MG-Jang/SAMSUNG-IOT-ROBOT-PJT-BOBI/HW/WAVEGO/version_0/코드 수정 후 적용.md

# 코드 수정 및 적용

- camera_opencv.py
- line:541
- robot.lookUp()을 여러번 추가하여 실제로 앉는 것 처럼 보여줌
```
elif act == 'up':
robot.lookUp()
robot.lookUp()
robot.lookUp()
robot.lookUp()
robot.lookUp()
robot.lookUp()
robot.lookUp()
```
