MG-Jang/SAMSUNG-IOT-ROBOT-PJT-BOBI/HW/DOCS/tips/[voice] setting_USB_mic.md

## USB 마이크 설정

USB 마이크를 라즈베리파이에 사용하기 위해서는 SW 혹은 패키지 따로 설치 안해줘도 된다.

우선, USB 마이크를 라즈베리파이 USB 포트에 연결한다.
다음 명령어를 통해 연결된 Port를 확인한다.
```
arecord -l
```
다음 이미지를 확인하면, card 2 즉 `2번 포트`에 USB 마이크가 꽂혀있는 것을 알 수 있다.

	
### USB 마이크 테스트

```
arecord --device=hw:2,0 --format S16_LE --rate 44100 -V mono -c1 voice.wav
```

> --device=hw:2는 2번 포트에 연결되어 있어 다음과 같이 작성했다.
voice.wav라는 파일에 음성파일 저장

해당 명령어를 실행시키면, `voice.wav`라는 파일이 생성되고, 해당 파일을 `mobaxterm` 좌측에서 더블클릭 혹은 윈도우로 복사 후 재생시켰다.

### 이슈 및 해결책
음성 녹음을 할 때, `볼륨이 매우 작은` 상태로 녹음이 되었다.
녹음 음량을 높일 수 있는 방법을 검색하여 해결책을 찾을 수 있었다.
 ```
 alsamixer
 ```
 을 통해 마이크 음량 조절가능하다.
 F6으로 오디오 선택 후 F5로 전체 조회 후 마우스 클릭으로 조절 가능하다.
