MG-Jang/SAMSUNG-IOT-ROBOT-PJT-BOBI/HW/DOCS/tips/[WAVEGO]senor_where_to_buy.md

# 센서 가격및 구매처

> 구매처: 송파 메이커스 페이스 (배송비 2700원)
- oled센서 i2c버전 2개: 3390*2
  - https://smartstore.naver.com/makerspace/products/2006471559

- ~~oled센서 spi버전(싸피1학기 떄 사용했던 것) : 4300 * 2~~
  - https://smartstore.naver.com/makerspace/products/2006472607

- 가스센서: 1980
  - https://smartstore.naver.com/makerspace/products/2006429718

- 터치센서: 300
  - https://smartstore.naver.com/makerspace/products/2667722657

- 스피커 지름 20mm : 200 (작동할지 모르겠지만 가격 리스크x)
  - https://smartstore.naver.com/makerspace/products/5784106870

- ~~DHT11(온습도 센서): 2000~~
  - https://smartstore.naver.com/makerspace/products/5010083549

추가 구매 사항
- 구리 방열판
- 빵판?
- 3핀

# wifi수신기

- http://itempage3.auction.co.kr/DetailView.aspx?ItemNo=C403515088&frm3=V2
  - 가격: 22400 무료 배송 
  - 장점:
    - 색상이 검정색이기 때문에 강아지 색상과도 일치
    - 크기가 작음
    - 광고 자체가 jetson nano 우분투 등 소형 컴퓨터 wifi수신기로 광고
    - 드라이버 설치x
    - 정확히 중앙에 있어 꼬리사용시 미관상 우수
  - 단점:
    - 기기명이 정확히 안나와있음.
    - 설명이 중국어로 적혀있어 의심이좀 감
  
- https://smartstore.naver.com/cotini/products/5220972886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
  - 가격: 19900 +3000(배송비)  // 현재 구매한다면 이제품을 생각
  - 장점: 
    - iptime 제조사이기 때문에 신뢰성 높음
    - 크기 작음
    - 드라이버 설치x
  - 단점:
    - 색상이 흰색이다.
    - 중앙 정렬이 약간 안되어있음.(봐줄만은 함)

- https://search.shopping.naver.com/catalog/26921391522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
  - 가격: 23400 + 3000(배송비 추정) 
    - 장점:
      - <span style="color:orange">가장 예쁘다!!!!!!. </span>
      - 브랜드 신뢰성 높음
      - wifi속도 가장 빠름
    - 단점:
      - 드라이버 설치가 필수!!!!!!!!!!!
      - 조금 비쌈?

# 스피커 
- https://www.coupang.com/vp/products/1421453945?itemId=2459973542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

# 라즈베리파이용 18650 배터리 쉴드
- 용도: 로봇에 장착된 배터리를 이용하여 esp32와 라즈베리파이가 통신할경우 통신에 문제가 발생하는 경우가 많다.(라즈베리파이에 충분한 전압이 공급되지 못하는 점과 gpio핀을 통해 공급하기 때문에 안정성도 떨어진다.) 따라서 추가 전력공급장치를 연결하여 안정적으로 라즈베리파이와 esp32가 통신 할 수 있도록 해준다.
-  https://smartstore.naver.com/bearfabmall/products/5240362851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
   -  특징
   -  배터리 1구
   -  무게 약 50~ 55g (배터리 포함) 
   -  no off가 가능할지? 

- https://smartstore.naver.com/makerspace/products/3537364484
  - 특징
    - 배터리 1구
    - on off 탑재
