MG-Jang/SAMSUNG-IOT-ROBOT-PJT-BOBI/HW/SENSORS/version_0/sensor pin.txt

OLED SDA : 2핀
SCL : 3핀

GAS : 15핀
DHT11 : 18핀
touch : 14핀

.
