MG-Jang/SAMSUNG-IOT-ROBOT-PJT-BOBI/HW/DOCS/ideas/[idea] web_essential_tech.md

### WEB

- 형태 : 웹 앱
- 타겟 사용자 : 부모님
- 기술스택
  - FE : HTML5, CSS3, Javascript, React.js, Node.js, PWA
  - BE : Python, Django
  - Server : MySQL, AWS S3
- 로그인
  - Google Login API
    - 영상을 스트리밍할 유튜브 계정 연동
  - 자체제작 로그인 API
- 1계정 1로봇 1디바이스
- qr코드를 통해 계정과 로봇과 연동
  - 가능한 경우 - 그렇지 않으면 연결 상태 일단 가정
- 기능
  - 기초 페이지
    - 앱 하단에 음성전송 토글을 활성화하면 앱 사용자가 음성을 녹음하고 비활성화하면 음성파일 형태로 서버에 저장하고 저장된 음성을 로봇에서 재생함 (카톡음성메시지랑 비슷한데 따로 재생버튼 안누르고 음성이 바로 나오는?)
      - 로봇에게 직접 통신으로 메시지를 보냈고 보낸 메시지 path 보내주기
    - 앱 상단에 실시간 로봇 배터리 잔량 표시기능 (충전 중일때는 잔량 표시없이 충전 중이라고만 표시할지)
  - 조작 페이지에서 로봇 전후좌우 이동 조작 가능 (기기와 직접 연결_인터넷)
    - 기초 조작: 좌/우/전진/후진 버튼 필요 (십자버튼)
      - 좌우-방향전환
      - 전후-전진/후진
    - 로봇에게 직접 통신으로 보내주기
  - 영상 스트리밍 기능
    - 유투브 계정과 연동
    - 웹캠으로 받아온 영상과 마이크로 받아온 음성을 합쳐서 유투브 라이브 형태로 실시간으로 스트리밍해서 보여주기 (음성 + 영상 합치는게 되는지 일단 해보자구)
  - 아카이브 기능
    - 스트리밍중인 영상을 실시간으로 캡처하여 아카이브에 저장하는 기능 ⇒가능? (기술 알아보기)
    - 스트리밍된 영상을 개인 유투브 스튜디오에서 편집해서 저장하고 저장된 영상의 링크와 그 영상의 썸네일을 아카이브 형태로 저장
  - 아이가 로봇을 통해 보낸 음성 메시지 조회 페이지 (미확인/확인 분류, 알림 팝업?)
    - 로봇에서 S3로 보낸 음성 메시지를 받아와 화면에서 출력
    - 로봇에서 새로운 메시지 알림을 받는 경우 데이터를 읽어오고 사용자에게 알림
  - 센서로 받아온 실시간 데이터를 보여주는 페이지
    - 현재 온도와 습도
    - 30분에 한 번  실시간으로 최신 데이터 출력
    - 일정 주기(30분? 1시간?)마다 저장된 온습도 값을 특정 기간동안 그래프 형태로 보여주는 기능
    - 가스 센서 - 1분마다 갱신되는 센서값에서 유해 가스값이 비정상적으로 높으면 반응(alert)
  - 로봇과의 친밀도를 나타내는 페이지
    - 특정 행동을 하면 친밀도 경험치가 쌓임
    - 경험치가 어느 정도 쌓이면 친밀도 레벨이 올라감
    - 친밀도 레벨에 따라 스토리와 가능한 행동들을 보여줌
    - 친밀도 레벨이 올라감에 따라 스토리와 로봇이 가능한 행동들이 점점 해금됨
    - 가능한 행동 리스트를 클릭하면 로봇이 그 행동을 하는 영상을 보여줌 (사전에 영상 녹화하여 삽입 (영상은 s3에 저장))
    - 1분마다 DB에 친밀도 update
  - 환경설정 페이지
    - 앱 테마 설정 : 기본모드 / 다크모드
    - 절전모드 설정 : 활성화시 로봇은 영상촬영을 비롯한 모든 행동을 멈추고 영상 촬영 및 스트리밍 진행과 눈 부분에 부착된 OLED에서 현재 시간만 보여줌
      - 절전모드 활성화, 비활성화 로봇에게 직접 통신으로 보내줌
    - 보비 음량 설정 : 보비 목소리 크기 조절
