MG-Jang/SAMSUNG-IOT-ROBOT-PJT-BOBI/DOCS/etc/bobi_always.jpg

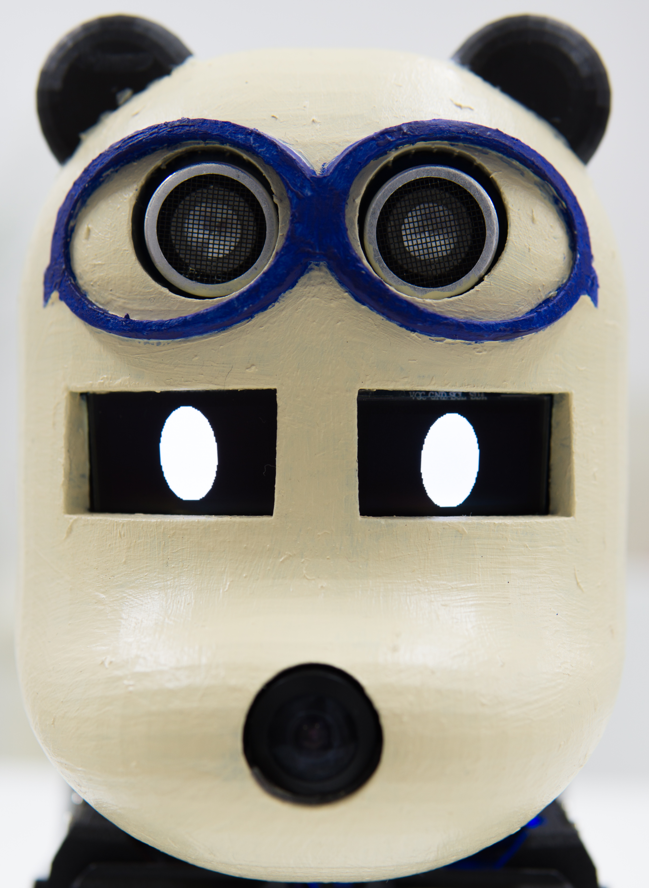
DOCS/etc/bobi_always.jpg
