MG-Jang/SAMSUNG-IOT-ROBOT-PJT-BOBI/DOCS/etc/bobi_mssg_fail.jpg

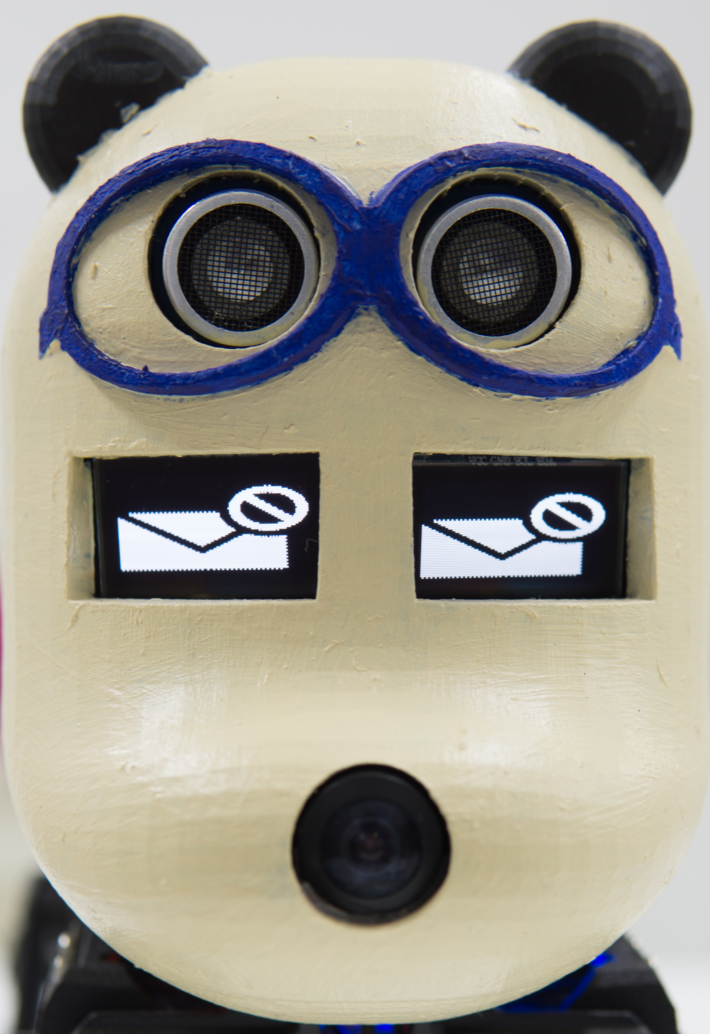
DOCS/etc/bobi_mssg_fail.jpg
