MG-Jang/SAMSUNG-IOT-ROBOT-PJT-BOBI/DOCS/etc/bobi_mssg_success.jpg

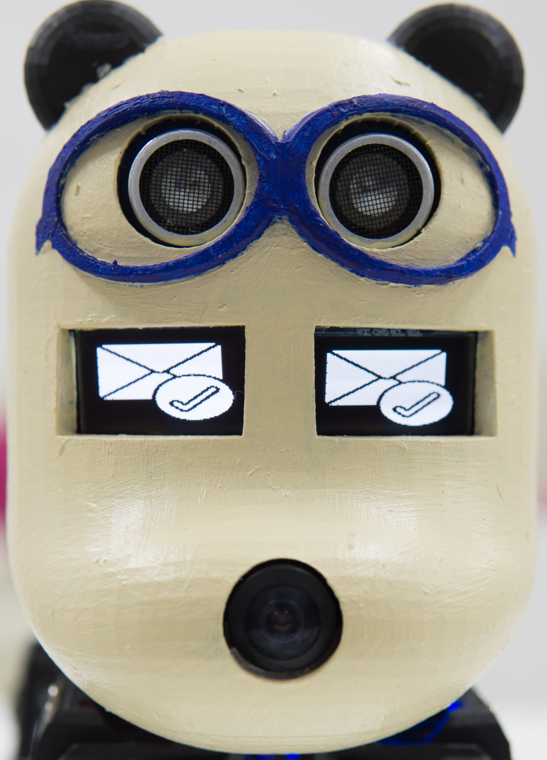
DOCS/etc/bobi_mssg_success.jpg
