MG-Jang/SAMSUNG-IOT-ROBOT-PJT-BOBI/DOCS/etc/bobi_smile.jpg

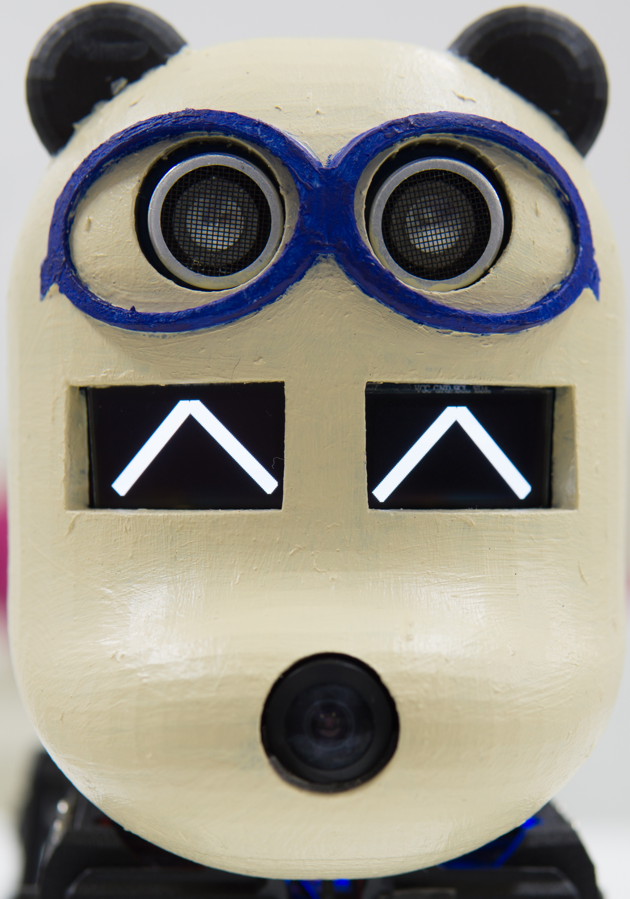
DOCS/etc/bobi_smile.jpg
