MG-Jang/SAMSUNG-IOT-ROBOT-PJT-BOBI/DOCS/etc/단체사진.jpg

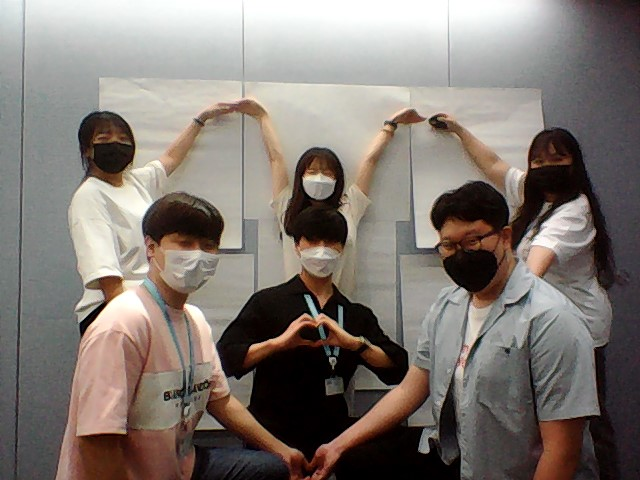
DOCS/etc/단체사진.jpg
