MG-Jang/SAMSUNG-IOT-ROBOT-PJT-BOBI/DOCS/etc/팀에게_바라는_점.jpg

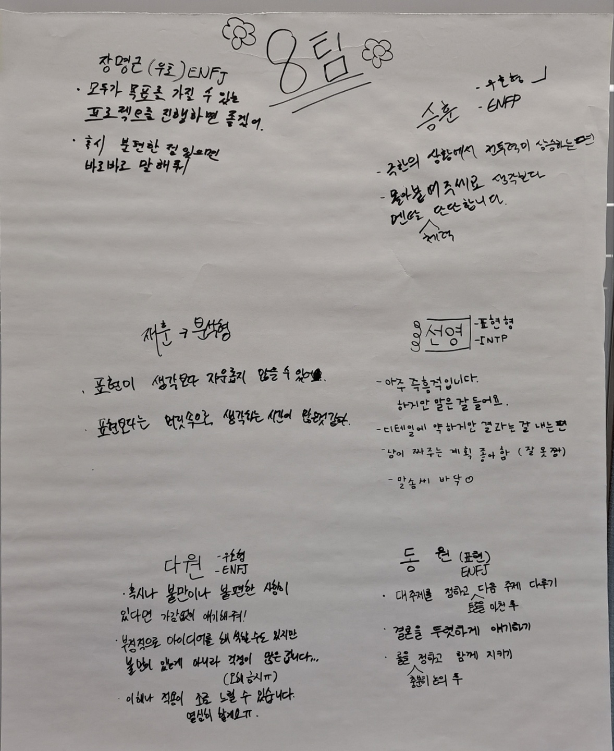
DOCS/etc/팀에게_바라는_점.jpg
