MG-Jang/SAMSUNG-IOT-ROBOT-PJT-BOBI/DOCS/ideas/[appearance] bobi_idea1.jpg

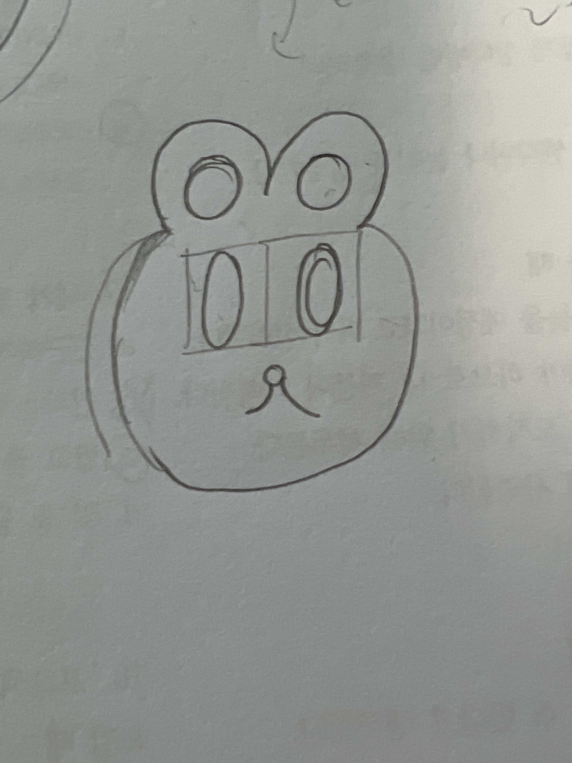
DOCS/ideas/[appearance] bobi_idea1.jpg
