MG-Jang/SAMSUNG-IOT-ROBOT-PJT-BOBI/DOCS/ideas/[appearance] bobi_idea2.jpg

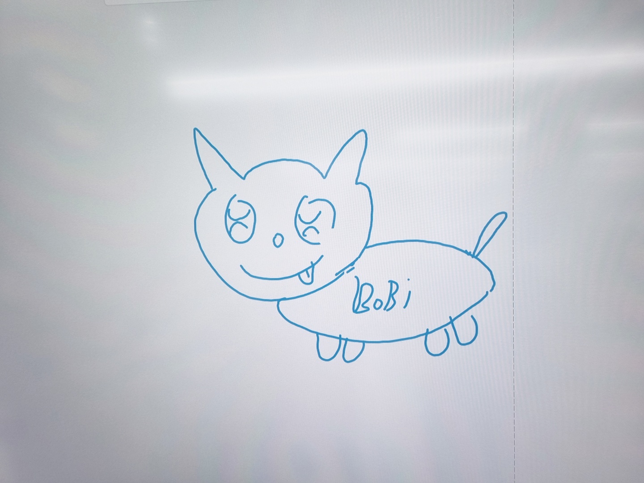
DOCS/ideas/[appearance] bobi_idea2.jpg
