MG-Jang/SAMSUNG-IOT-ROBOT-PJT-BOBI/DOCS/ideas/[appearance] bobi_idea4.jpg

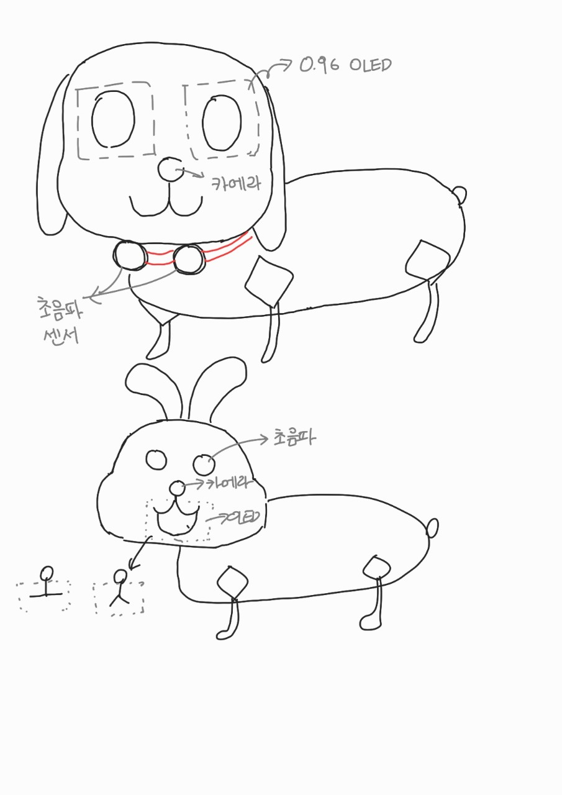
DOCS/ideas/[appearance] bobi_idea4.jpg
