MG-Jang/SAMSUNG-IOT-ROBOT-PJT-BOBI/DOCS/ideas/[appearance] bobi_idea5.jpg

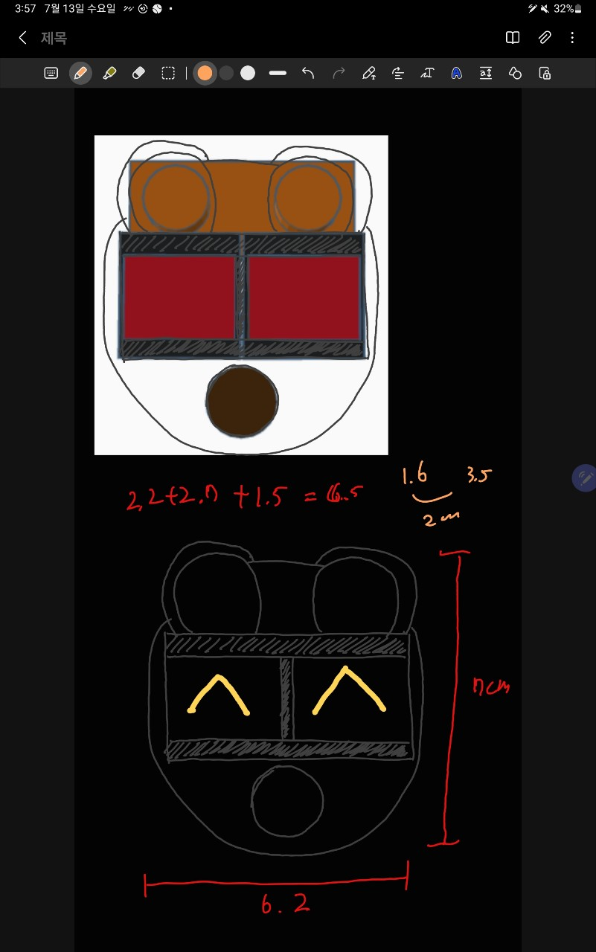
DOCS/ideas/[appearance] bobi_idea5.jpg
