MG-Jang/SAMSUNG-IOT-ROBOT-PJT-BOBI/DOCS/ideas/[DB] 0718_ERD.png

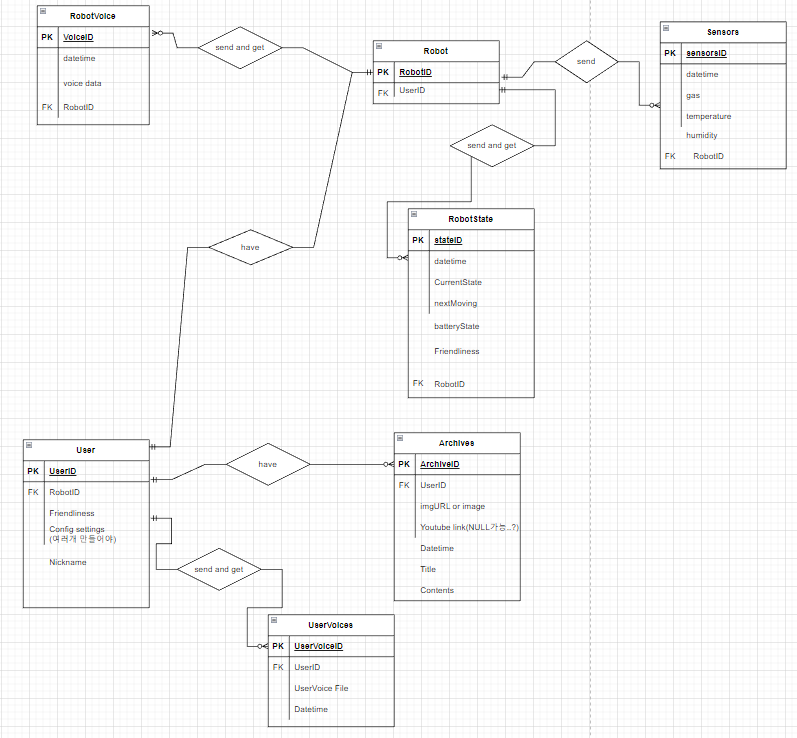
DOCS/ideas/[DB] 0718_ERD.png
