MG-Jang/SAMSUNG-IOT-ROBOT-PJT-BOBI/DOCS/ideas/[DB] 0719_ERD.jpg

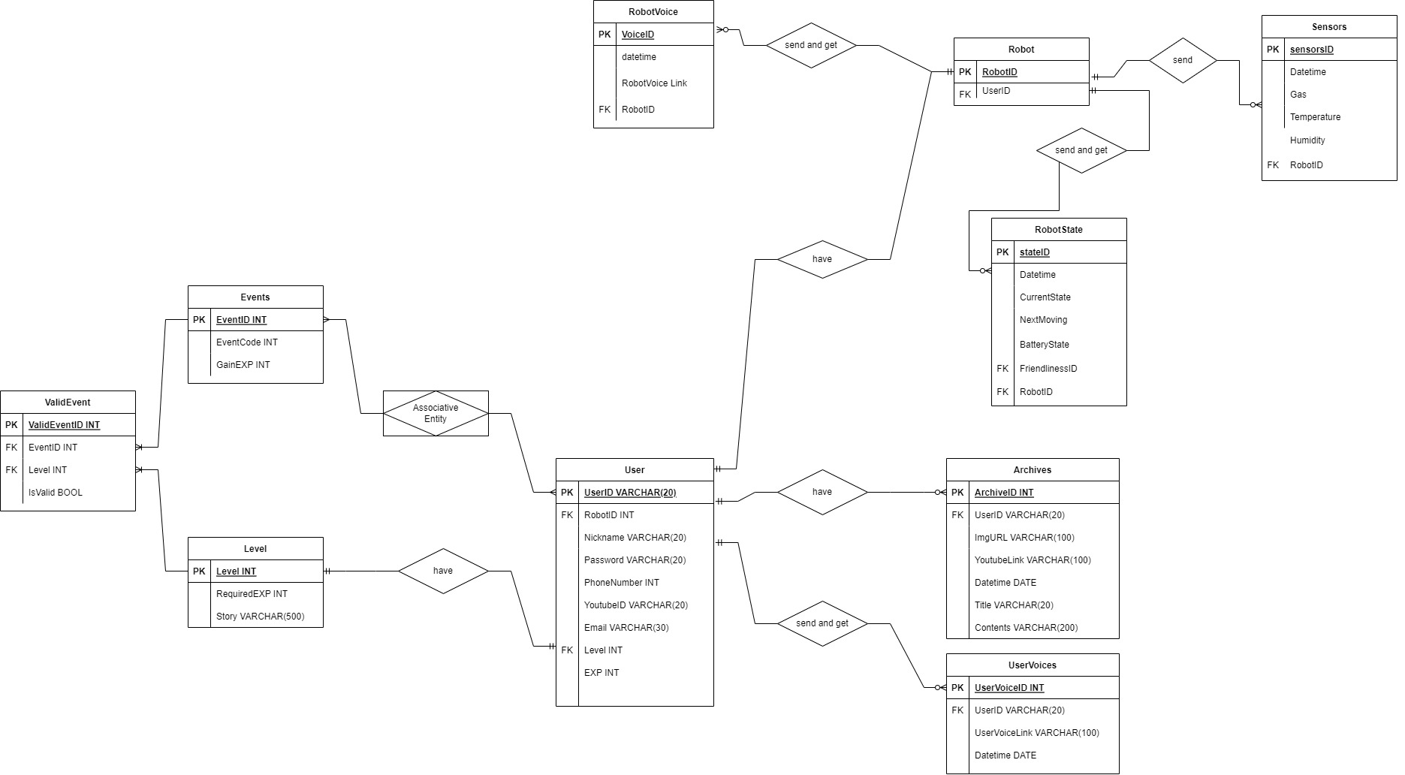
DOCS/ideas/[DB] 0719_ERD.jpg
