MG-Jang/SAMSUNG-IOT-ROBOT-PJT-BOBI/WEB/BE/README.assets/image-20220818151705240.png

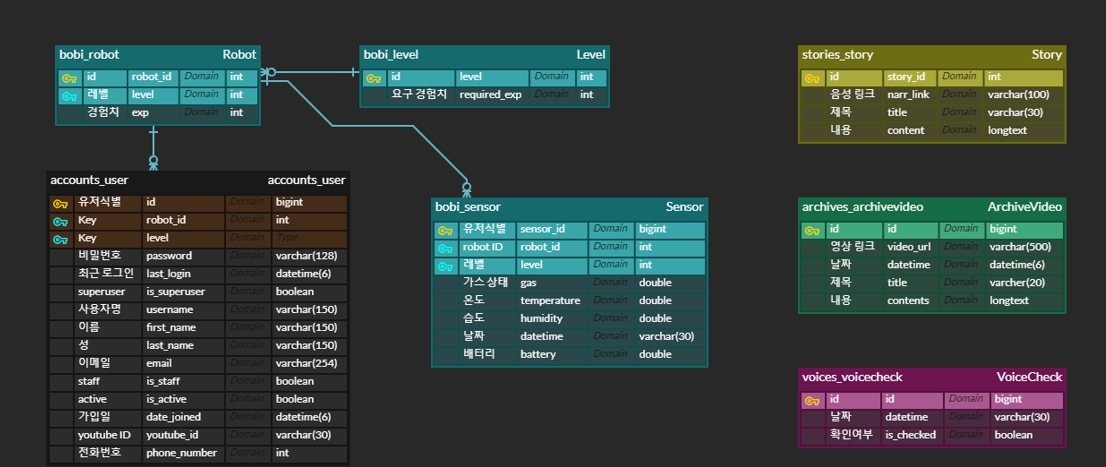
WEB/BE/README.assets/image-20220818151705240.png
