MG-Jang/SAMSUNG-IOT-ROBOT-PJT-BOBI/WEB/BE/README.assets/image-20220818172745645.png

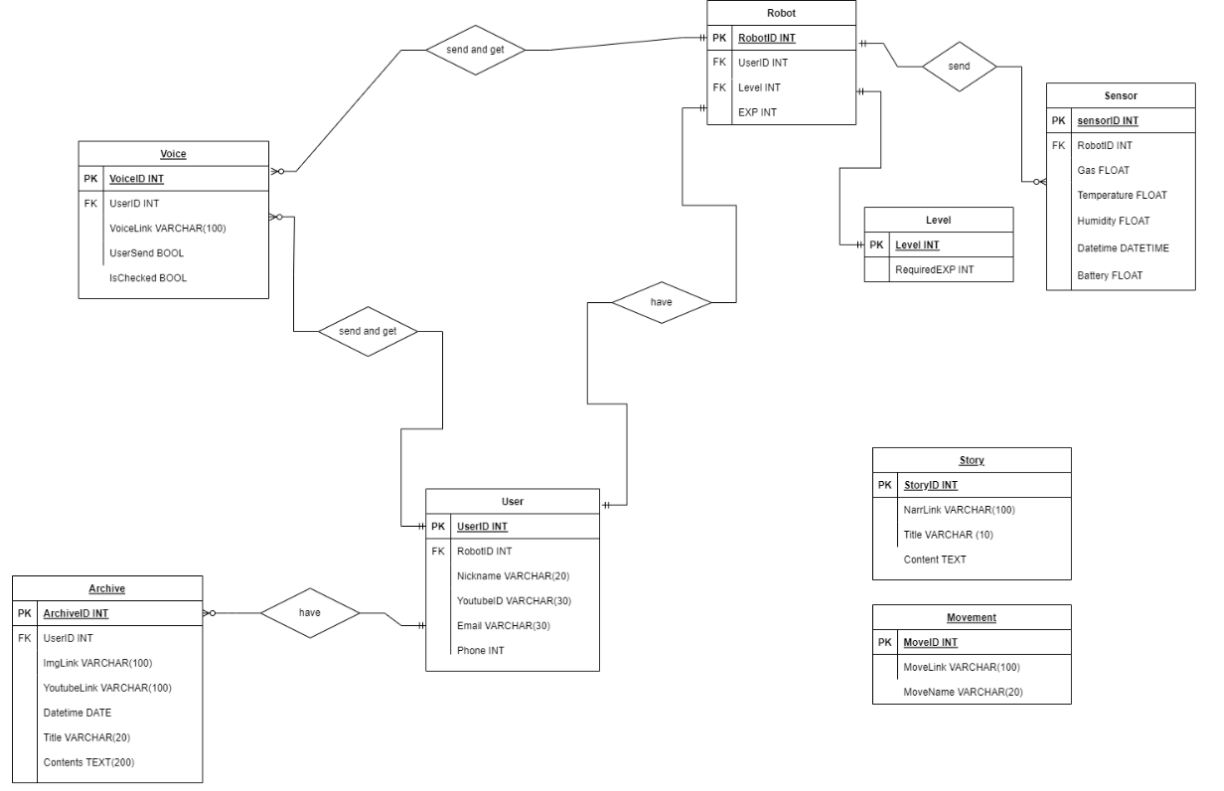
WEB/BE/README.assets/image-20220818172745645.png
