MG-Jang/SAMSUNG-IOT-ROBOT-PJT-BOBI/WEB/FE + BE/bobi_backup/README.assets/image-20220818011454465.png

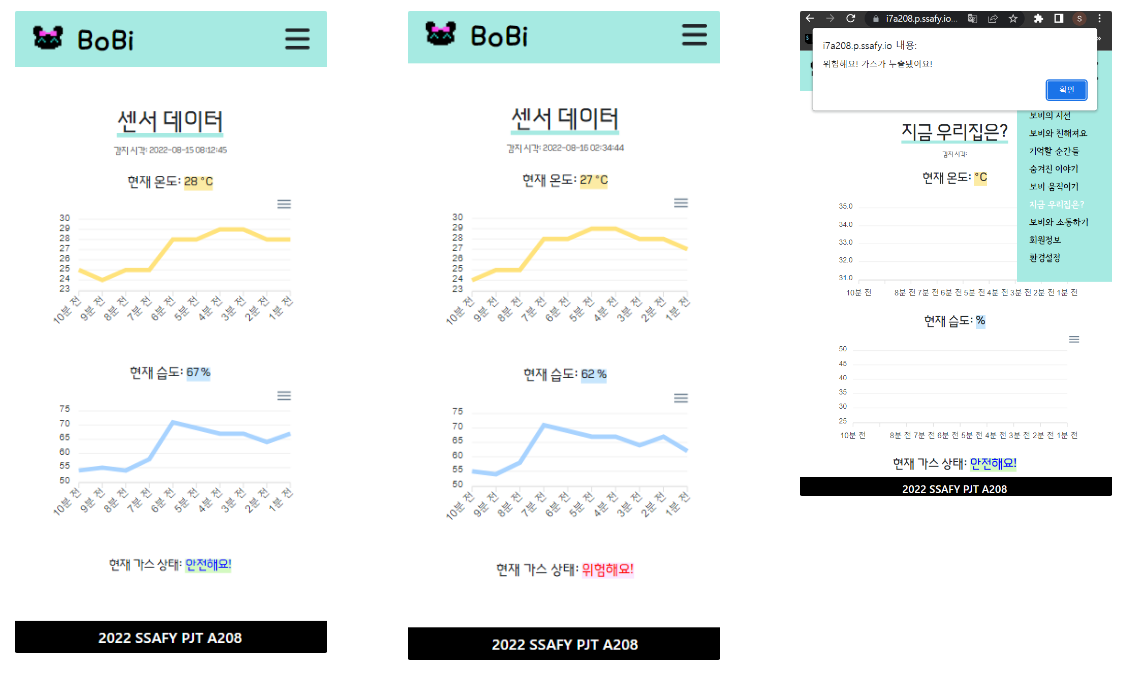
WEB/FE + BE/bobi_backup/README.assets/image-20220818011454465.png
