MG-Jang/SAMSUNG-IOT-ROBOT-PJT-BOBI/WEB/FE/DOCS/ideas/[layout] 0714_initial_layout.png

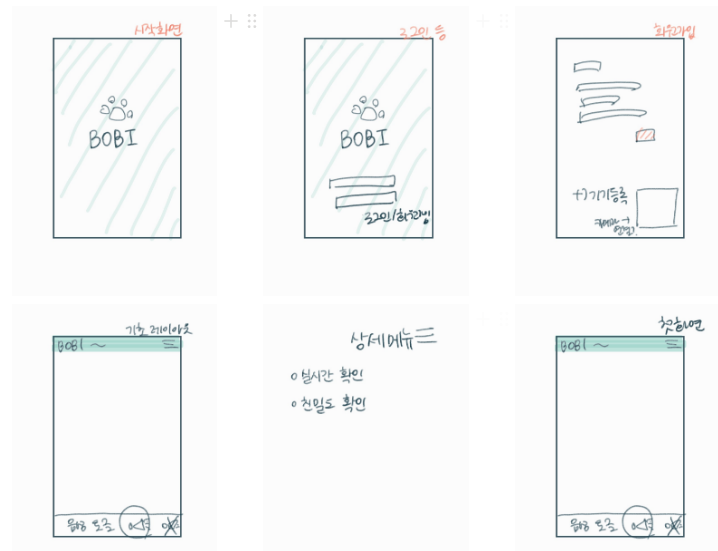
WEB/FE/DOCS/ideas/[layout] 0714_initial_layout.png
