MG-Jang/SAMSUNG-IOT-ROBOT-PJT-BOBI/WEB/FE/DOCS/ideas/[layout] 0714_pages.jpg

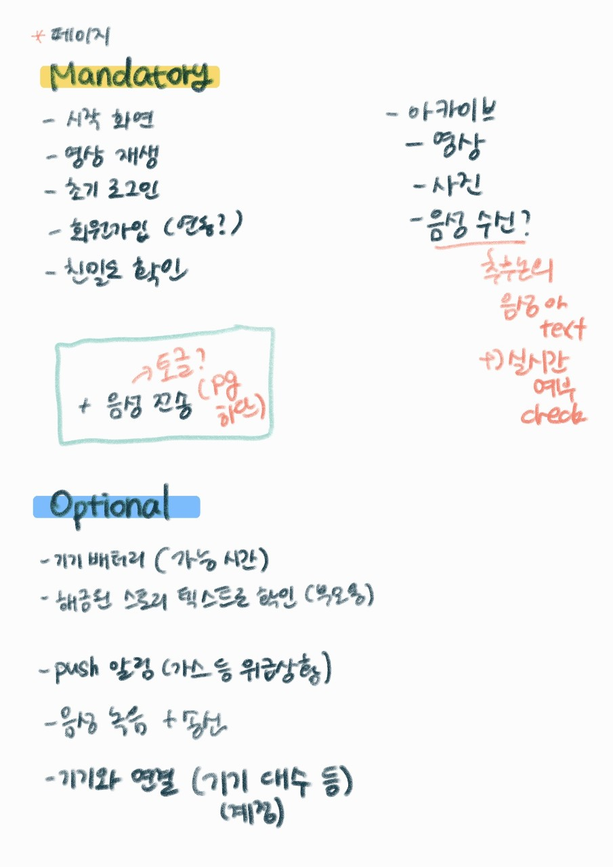
WEB/FE/DOCS/ideas/[layout] 0714_pages.jpg
