MG-Jang/SAMSUNG-IOT-ROBOT-PJT-BOBI/WEB/FE/README.assets/image-20220818002039471.png

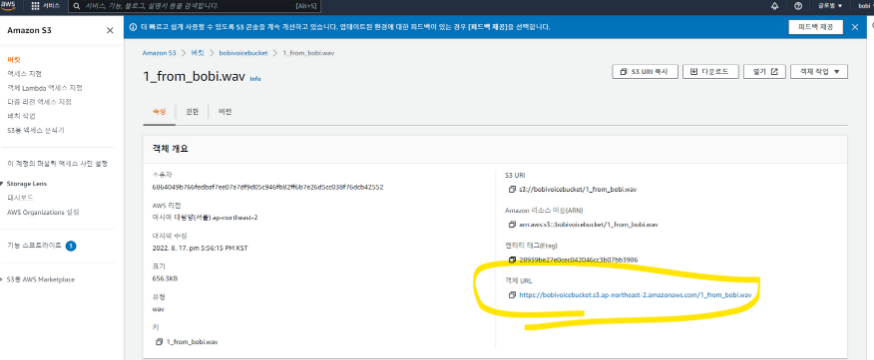
WEB/FE/README.assets/image-20220818002039471.png
