MG-Jang/SAMSUNG-IOT-ROBOT-PJT-BOBI/WEB/README.assets/image-20220819102034384.png

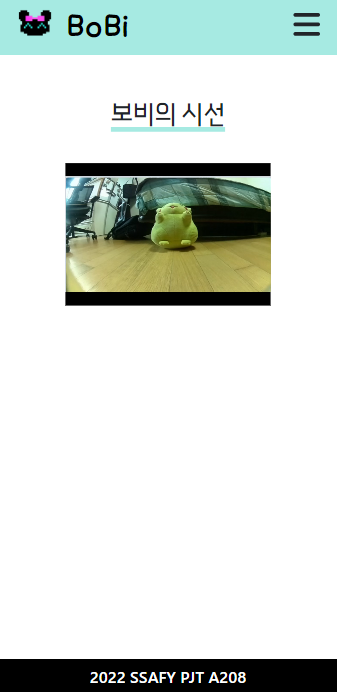
WEB/README.assets/image-20220819102034384.png
