MG-Jang/SAMSUNG-IOT-ROBOT-PJT-BOBI/DOCS/tips/[git] basic_guide.assets/image-20220711194625866.png

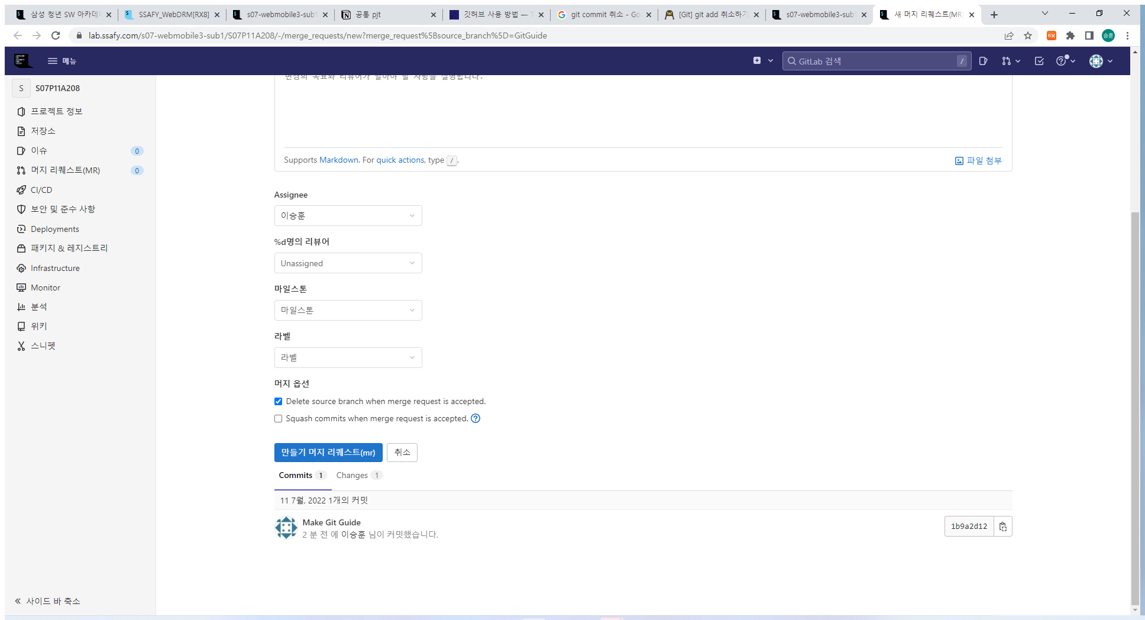
DOCS/tips/[git] basic_guide.assets/image-20220711194625866.png
