MG-Jang/SAMSUNG-IOT-ROBOT-PJT-BOBI/DOCS/tips/[git] basic_guide.assets/image-20220711195616462.png

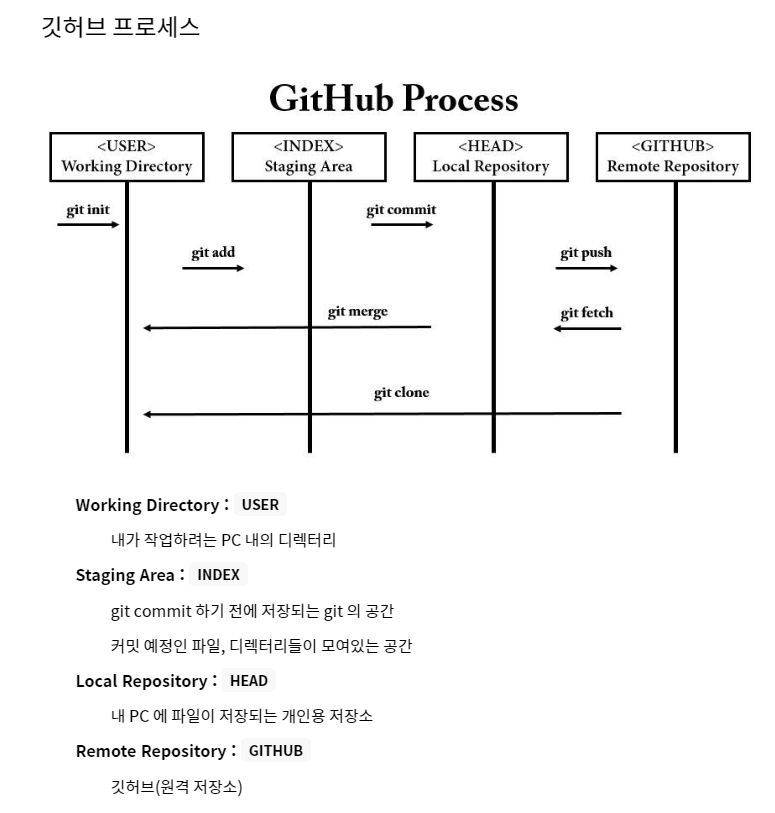
DOCS/tips/[git] basic_guide.assets/image-20220711195616462.png
