MG-Jang/SAMSUNG-IOT-ROBOT-PJT-BOBI/HW/VOICE_DETECTION/voice.py

import os
import voice_porcupine_custom
import sys
import time
from threading import Thread
from voice_recognition import VoiceRecognition


class DetectHotword(Thread):
    def __init__(self, user_id):
        Thread.__init__(self)
        self.kill_received = False
        self.user_id = user_id
        self.stt = VoiceRecognition(self.user_id)
    def run(self):
        while not self.kill_received:
            if(voice_porcupine_custom.hot_word_flag):
                print("Hotword detected")
                self.stt.run()
                time.sleep(7)


def has_live_threads(threads):
    for t in threads:
        if t.is_alive():
            return True


if __name__ == "__main__":
    args = voice_porcupine_custom.porcupine_parsing()
    threads = []
    th1 = voice_porcupine_custom.PorcupineCustom(
        access_key=args.access_key,
        library_path=args.library_path,
        model_path=args.model_path,
        keyword_paths=args.keyword_paths,
        sensitivities=args.sensitivities,
        output_path=args.output_path,
        input_device_index=args.audio_device_index)

    th2 = DetectHotword(args.user_id)
    threads.append(th1)
    threads.append(th2)
    th1.start()
    th2.start()

    while has_live_threads(threads):
        try:
            for t in threads:
                if t is not None and t.is_alive():
                    t.join(1)
        except KeyboardInterrupt:
            print("Sending kill to threads")
            for t in threads:
                t.kill_received = True

            for t in threads:
                if t is not None and t.is_alive():
                    t.join(1)

    print("Exited")
