MG-Jang/SAMSUNG-IOT-ROBOT-PJT-BOBI/HW/VOICE_DETECTION/voice_porcupine_custom.py

'''
# Copyright 2018-2021 Picovoice Inc.
#
# You may not use this file except in compliance with the license. A copy of the license is located in the "LICENSE"
# file accompanying this source.
#
# Unless required by applicable law or agreed to in writing, software distributed under the License is distributed on
# an "AS IS" BASIS, WITHOUT WARRANTIES OR CONDITIONS OF ANY KIND, either express or implied. See the License for the
# specific language governing permissions and limitations under the License.
#

# Modification history
#   Created by Dongwon Kim on 04 Aug, 2022 
#   Modified by Dongwon Kim on 11 Aug, 2022
#
# reference 
#   picovoice's porcupine_demo_mic.py
'''
import argparse
import os
import struct
import wave
from datetime import datetime
from threading import Thread

import pvporcupine
from pvrecorder import PvRecorder

# flag for hot word detection, reading in voice.py
hot_word_flag = 0

class PorcupineCustom(Thread):
    def __init__(
            self,
            access_key,
            library_path,
            sensitivities,
            model_path='/home/pi/WAVEGO/RPi/voice_data/porcupine_params_ko.pv',
            keyword_paths='/home/pi//WAVEGO/RPi/voice_data/hi_bobi_ko_rpi.ppn',
            input_device_index=None,
            output_path=None):
        """
        Constructor.
        :param library_path: Absolute path to Porcupine's dynamic library.
        :param model_path: Absolute path to the file containing model parameters.
        :param keyword_paths: Absolute paths to keyword model files.
        :param sensitivities: Sensitivities for detecting keywords. Each value should be a number within [0, 1]. A
        higher sensitivity results in fewer misses at the cost of increasing the false alarm rate. If not set 0.5 will
        be used.
        :param input_device_index: Optional argument. If provided, audio is recorded from this input device. Otherwise,
        the default audio input device is used.
        :param output_path: If provided recorded audio will be stored in this location at the end of the run.
        """

        super(PorcupineCustom, self).__init__()

        self._access_key = access_key
        self._library_path = library_path
        self._model_path = model_path
        self._keyword_paths = keyword_paths
        self._sensitivities = sensitivities
        self._input_device_index = input_device_index

        self._output_path = output_path
        self.kill_received = False # for terminating thread

    def run(self):
        """
         Creates an input audio stream, instantiates an instance of Porcupine object, and monitors the audio stream for
         occurrences of the wake word(s). It prints the time of detection for each occurrence and the wake word.
         
         execute while the thread is alive
         """
        while not self.kill_received:
            global hot_word_flag
            keywords = list()
            for x in self._keyword_paths:
                keyword_phrase_part = os.path.basename(
                    x).replace('.ppn', '').split('_')
                if len(keyword_phrase_part) > 6:
                    keywords.append(' '.join(keyword_phrase_part[0:-6]))
                else:
                    keywords.append(keyword_phrase_part[0])

            porcupine = None
            recorder = None
            wav_file = None
            try:
                porcupine = pvporcupine.create(
                    access_key=self._access_key,
                    library_path=self._library_path,
                    model_path=self._model_path,
                    keyword_paths=self._keyword_paths,
                    sensitivities=self._sensitivities)

                recorder = PvRecorder(
                    device_index=self._input_device_index, frame_length=porcupine.frame_length)
                recorder.start()

                if self._output_path is not None:
                    wav_file = wave.open(self._output_path, "w")
                    wav_file.setparams((1, 2, 16000, 512, "NONE", "NONE"))

                print('Using device: %s', recorder.selected_device)

                print('Listening {')
                for keyword, sensitivity in zip(keywords, self._sensitivities):
                    print('  %s (%.2f)' % (keyword, sensitivity))
                print('}')

                while True:
                    pcm = recorder.read()

                    if wav_file is not None:
                        wav_file.writeframes(struct.pack("h" * len(pcm), *pcm))

                    result = porcupine.process(pcm)
                    # set hot word flag
                    if result >= 0:
                        hot_word_flag = 1
                        print('[%s] Detected %s' %
                              (str(datetime.now()), keywords[result]))
                    else:
                        hot_word_flag = 0
            except pvporcupine.PorcupineInvalidArgumentError as e:
                args = (
                    self._access_key,
                    self._library_path,
                    self._model_path,
                    self._keyword_paths,
                    self._sensitivities,
                )
                print("One or more arguments provided to Porcupine is invalid: ", args)
                print("If all other arguments seem valid, ensure that '%s' is a valid AccessKey" %
                      self._access_key)
                raise e
            except pvporcupine.PorcupineActivationError as e:
                print("AccessKey activation error")
                raise e
            except pvporcupine.PorcupineActivationLimitError as e:
                print("AccessKey '%s' has reached it's temporary device limit" %
                      self._access_key)
                raise e
            except pvporcupine.PorcupineActivationRefusedError as e:
                print("AccessKey '%s' refused" % self._access_key)
                raise e
            except pvporcupine.PorcupineActivationThrottledError as e:
                print("AccessKey '%s' has been throttled" % self._access_key)
                raise e
            except pvporcupine.PorcupineError as e:
                print("Failed to initialize Porcupine")
                raise e
            except KeyboardInterrupt:
                print('Stopping ...')
            finally:
                if porcupine is not None:
                    porcupine.delete()

                if recorder is not None:
                    recorder.delete()

                if wav_file is not None:
                    wav_file.close()

    @classmethod
    def show_audio_devices(cls):
        devices = PvRecorder.get_audio_devices()

        for i in range(len(devices)):
            print('index: %d, device name: %s' % (i, devices[i]))


def porcupine_parsing():
    """Parse the args and check if nessesary args are given

    Raises:
        ValueError: access key of porcupine is required
        ValueError: keywords or keywords_paths should be given
        ValueError: sensitivities should be defined for all keywords

    Returns:
        args: parsed arguements 
    """
    parser = argparse.ArgumentParser()

    parser.add_argument('--access_key',
                        help='AccessKey obtained from Picovoice Console (https://console.picovoice.ai/)')

    parser.add_argument(
        '--keywords',
        nargs='+',
        help='List of default keywords for detection. Available keywords: %s' % ', '.join(
            sorted(pvporcupine.KEYWORDS)),
        choices=sorted(pvporcupine.KEYWORDS),
        metavar='')

    parser.add_argument(
        '--keyword_paths',
        nargs='+',
        help="Absolute paths to keyword model files. If not set it will be populated from `--keywords` argument")

    parser.add_argument(
        '--library_path', help='Absolute path to dynamic library.', default=pvporcupine.LIBRARY_PATH)

    parser.add_argument(
        '--model_path',
        help='Absolute path to the file containing model parameters.',
        default=pvporcupine.MODEL_PATH)

    parser.add_argument(
        '--sensitivities',
        nargs='+',
        help="Sensitivities for detecting keywords. Each value should be a number within [0, 1]. A higher " +
             "sensitivity results in fewer misses at the cost of increasing the false alarm rate. If not set 0.5 " +
             "will be used.",
        type=float,
        default=None)

    parser.add_argument('--audio_device_index',
                        help='Index of input audio device.', type=int, default=-1)

    parser.add_argument(
        '--output_path', help='Absolute path to recorded audio for debugging.', default=None)

    parser.add_argument('--show_audio_devices', action='store_true')

    parser.add_argument('--user_id',
                        help="User ID registered in DB in integer")

    args = parser.parse_args()

    if args.show_audio_devices:
        PorcupineCustom.show_audio_devices()
    else:
        if args.access_key is None:
            raise ValueError("AccessKey (--access_key) is required")
        if args.keyword_paths is None:
            if args.keywords is None:
                raise ValueError(
                    "Either `--keywords` or `--keyword_paths` must be set.")

            keyword_paths = [pvporcupine.KEYWORD_PATHS[x]
                             for x in args.keywords]
            args.keyword_paths = keyword_paths
        else:
            keyword_paths = args.keyword_paths

        if args.sensitivities is None:
            args.sensitivities = [0.5] * len(keyword_paths)

        if len(keyword_paths) != len(args.sensitivities):
            raise ValueError(
                'Number of keywords does not match the number of sensitivities.')

        return args
