MG-Jang/SAMSUNG-IOT-ROBOT-PJT-BOBI/WEB/BE/DOCKERIZE_REAL/backend/web/bobi/serializers.py

from rest_framework import serializers
from .models import Robot, Level, Sensor

class RobotSerializer(serializers.ModelSerializer):
    class Meta:
        model = Robot
        fields = '__all__'

class LevelSerializer(serializers.ModelSerializer):
    class Meta:
        model = Level
        fields = '__all__'

class SensorSerializer(serializers.ModelSerializer):
    class Meta:
        model = Sensor
        fields = '__all__'
